kadonstimpson/ROM-dumper/Src/uart.c

#include "uart.h"
#include "stm32f0xx.h"
#include "stm32f0xx_hal.h"
#include <string.h>
#include <unistd.h>

UART_HandleTypeDef huart1;

void GPIO_UART1_Init(void) {
    __HAL_RCC_GPIOA_CLK_ENABLE();

    GPIO_InitTypeDef GPIO_InitStruct = {0};

    // PA9 = USART1_TX, PA10 = USART1_RX
    GPIO_InitStruct.Pin = GPIO_PIN_9 | GPIO_PIN_10;
    GPIO_InitStruct.Mode = GPIO_MODE_AF_PP; 
    GPIO_InitStruct.Pull = GPIO_NOPULL;
    GPIO_InitStruct.Speed = GPIO_SPEED_FREQ_HIGH;
    GPIO_InitStruct.Alternate = GPIO_AF1_USART1; 

    HAL_GPIO_Init(GPIOA, &GPIO_InitStruct);
}

void UART1_Init(void) {
    __HAL_RCC_USART1_CLK_ENABLE();

    huart1.Instance = USART1;
    huart1.Init.BaudRate = 115200;
    huart1.Init.WordLength = UART_WORDLENGTH_8B;
    huart1.Init.StopBits = UART_STOPBITS_1;
    huart1.Init.Parity = UART_PARITY_NONE;
    huart1.Init.Mode = UART_MODE_TX_RX;

    HAL_UART_Init(&huart1);
}

void send_serial(const char* msg) {
    HAL_UART_Transmit(&huart1, (uint8_t*)msg, strlen(msg), HAL_MAX_DELAY);
}

// Allow printf over USART

int _write(int file, char *ptr, int len)
{
    if (file == STDOUT_FILENO || file == STDERR_FILENO) {
        HAL_UART_Transmit(&huart1, (uint8_t *)ptr, len, HAL_MAX_DELAY);
        return len;
    }
    return -1;
}
